NileshAm/RoboGames-TeamLynx/sheet metal parts/Back horizontal brace.SLDPRT

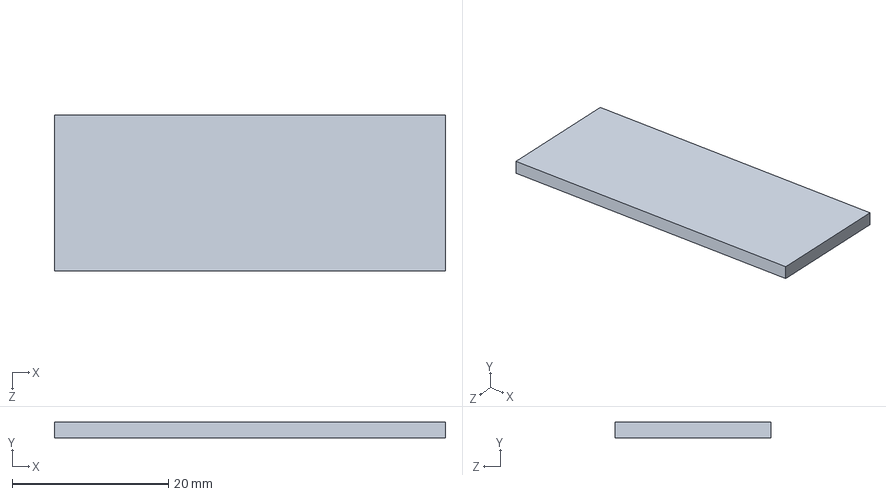
[picture p18: CAD file, 2025-09-17]
sheet metal parts/Back horizontal brace.SLDPRT
50.0 x 2.00 x 20.0 mm
