NileshAm/RoboGames-TeamLynx/downloads/avian-4250-800kv-outrunner-brushless-motor-1.snapshot.3/Outrunner Motor/MotorCrossBar.SLDPRT

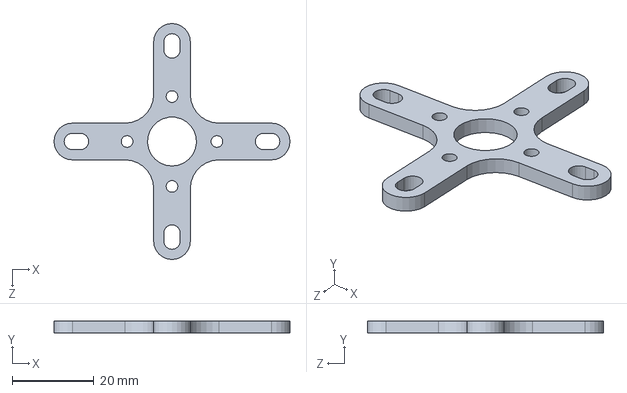
[picture p19: CAD file, 2025-09-02]
downloads/avian-4250-800kv-outrunner-brushless-motor-1.snapshot.3/Outrunner Motor/MotorCrossBar.SLDPRT
57.8 x 3.00 x 57.8 mm
