NileshAm/RoboGames-TeamLynx/laserCutFiles/motor mount sprocket.DXF

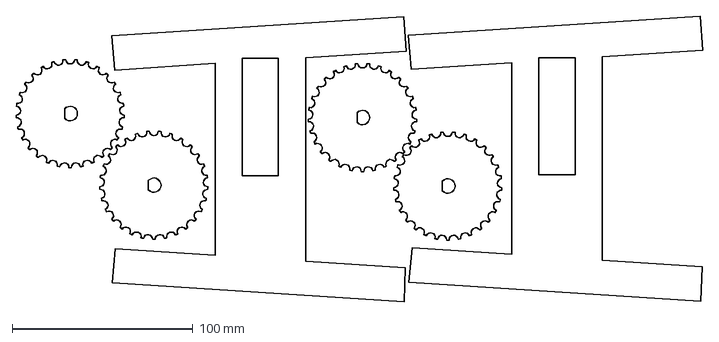
[picture p20: CAD file, 2025-09-11]
laserCutFiles/motor mount sprocket.DXF
380.6 x 158.4 mm
