NileshAm/RoboGames-TeamLynx/Parts/Sproket.SLDPRT

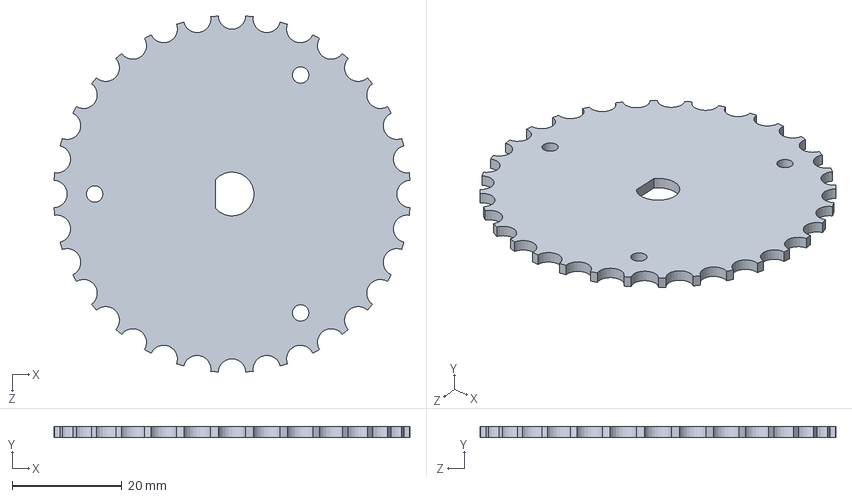
[picture p21: CAD file, 2026-03-14]
Parts/Sproket.SLDPRT
64.8 x 2.00 x 64.8 mm
