NileshAm/RoboGames-TeamLynx/sheet metal parts/Back brace.SLDPRT

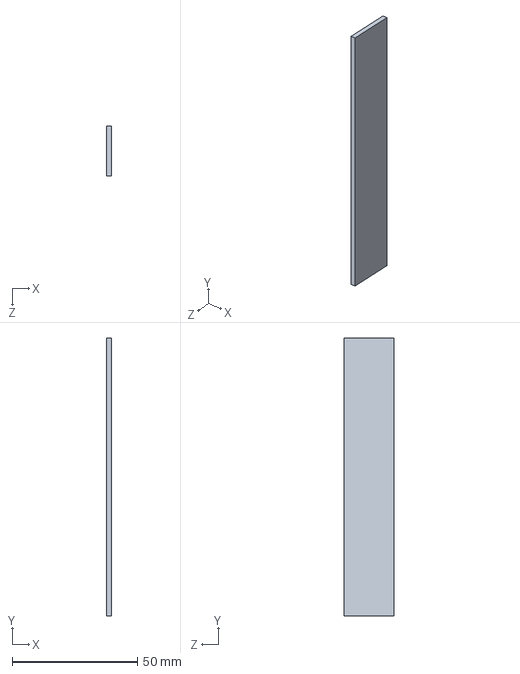
[picture p22: CAD file, 2025-09-17]
sheet metal parts/Back brace.SLDPRT
2.00 x 111.0 x 20.0 mm
