NileshAm/RoboGames-TeamLynx/downloads/avian-4250-800kv-outrunner-brushless-motor-1.snapshot.3/Outrunner Motor/SimpleBearing.SLDPRT

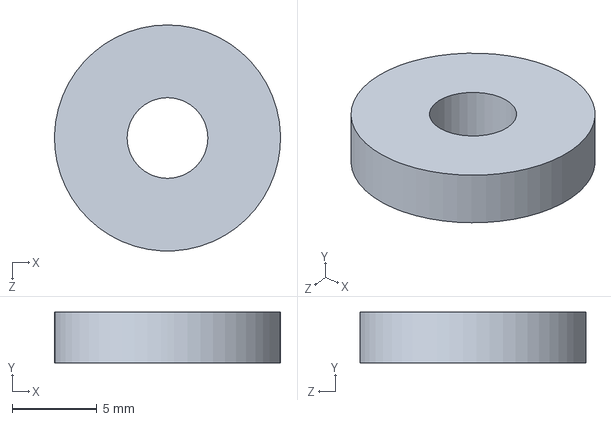
[picture p24: CAD file, 2025-09-02]
downloads/avian-4250-800kv-outrunner-brushless-motor-1.snapshot.3/Outrunner Motor/SimpleBearing.SLDPRT
13.3 x 3.00 x 13.3 mm
