NileshAm/RoboGames-TeamLynx/sheet metal parts/Bottom brace.SLDPRT

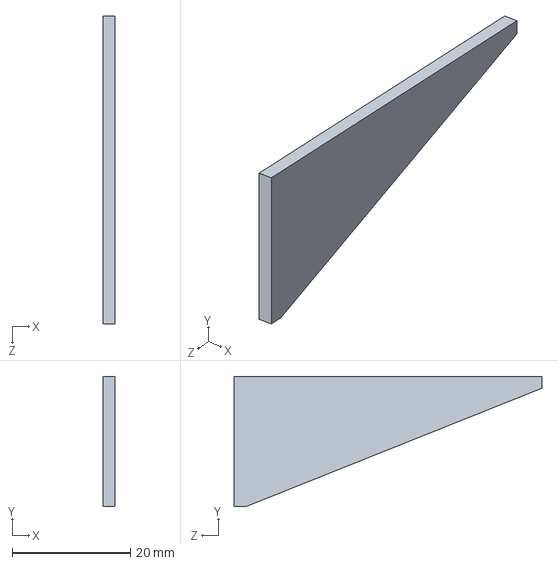
[picture p25: CAD file, 2025-09-17]
sheet metal parts/Bottom brace.SLDPRT
2.00 x 22.0 x 52.0 mm
