NileshAm/RoboGames-TeamLynx/downloads/avian-4250-800kv-outrunner-brushless-motor-1.snapshot.3/Outrunner Motor/Outrunner Brushless Motor Top.SLDPRT

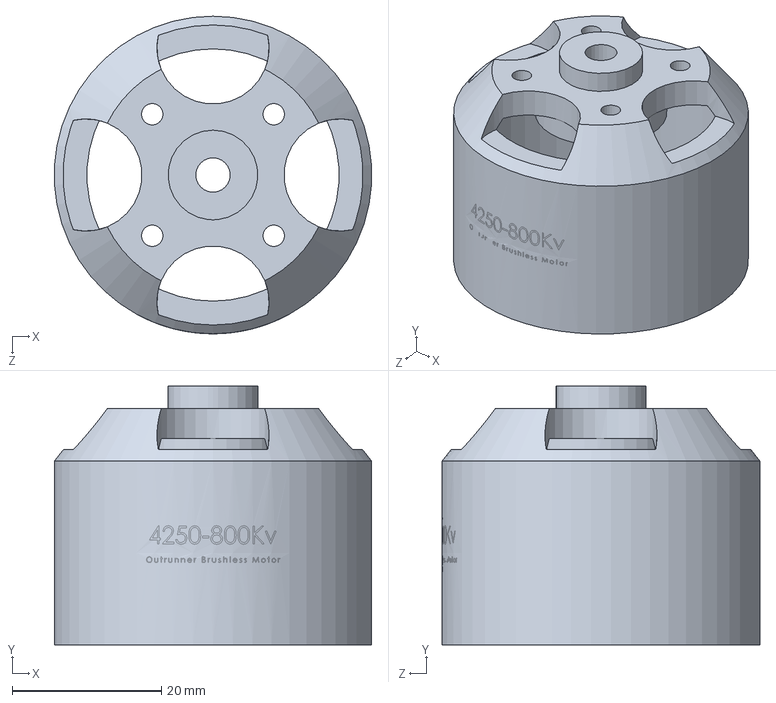
[picture p26: CAD file, 2025-09-02]
downloads/avian-4250-800kv-outrunner-brushless-motor-1.snapshot.3/Outrunner Motor/Outrunner Brushless Motor Top.SLDPRT
42.4 x 34.6 x 42.5 mm
