NileshAm/RoboGames-TeamLynx/downloads/avian-4250-800kv-outrunner-brushless-motor-1.snapshot.3/Outrunner Motor/PropShaft.SLDPRT

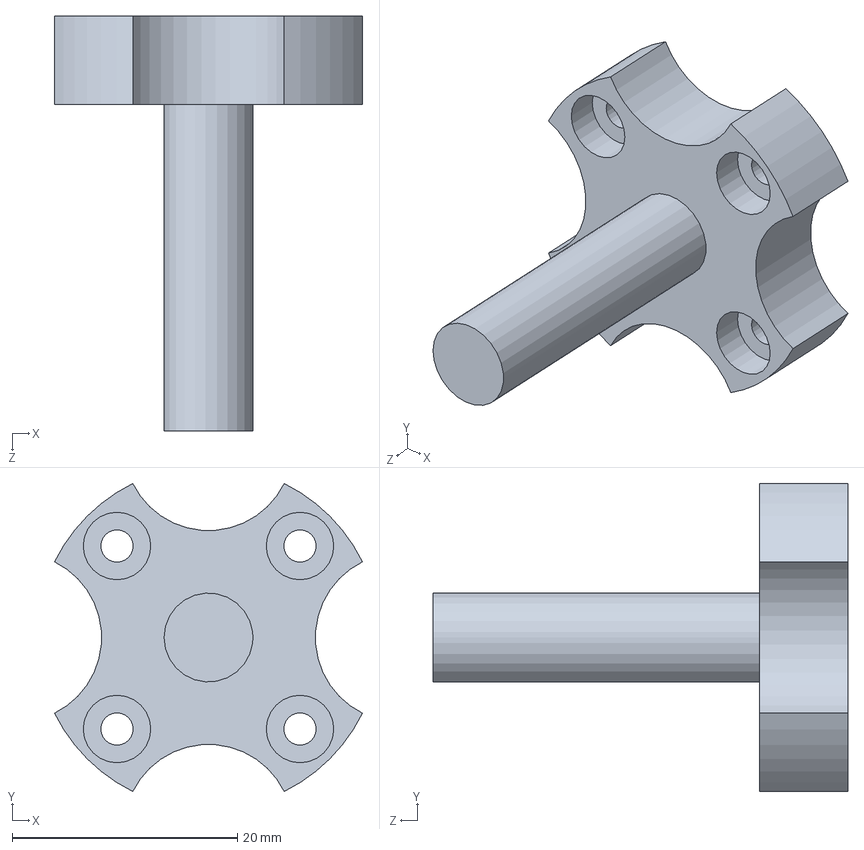
[picture p28: CAD file, 2025-09-02]
downloads/avian-4250-800kv-outrunner-brushless-motor-1.snapshot.3/Outrunner Motor/PropShaft.SLDPRT
27.4 x 27.4 x 36.9 mm
