NileshAm/RoboGames-TeamLynx/Parts/BladeMotorMount.SLDPRT

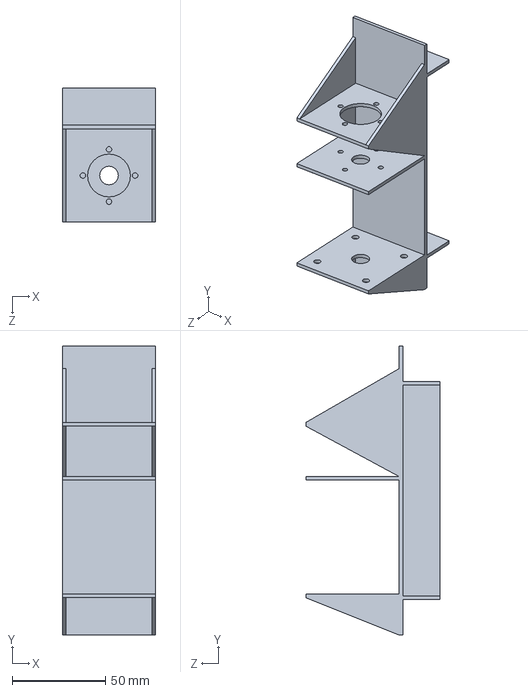
[picture p29: CAD file, 2025-09-17]
Parts/BladeMotorMount.SLDPRT
50.0 x 155.0 x 72.0 mm
