NileshAm/RoboGames-TeamLynx/sheet metal parts/Top brace.SLDPRT

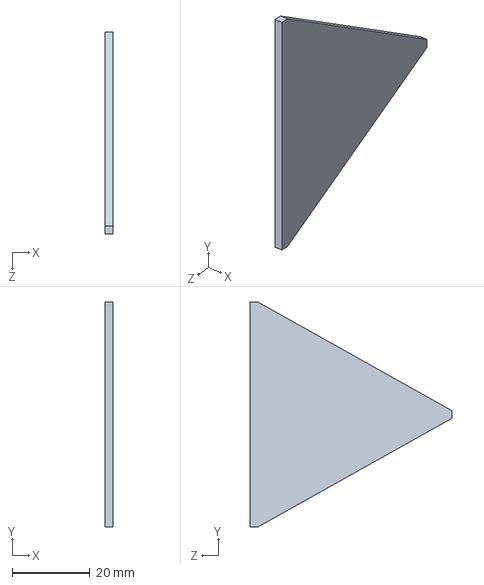
[picture p30: CAD file, 2025-09-17]
sheet metal parts/Top brace.SLDPRT
2.00 x 58.0 x 52.0 mm
