NileshAm/RoboGames-TeamLynx/sheet metal parts/motor mount level 2.SLDPRT

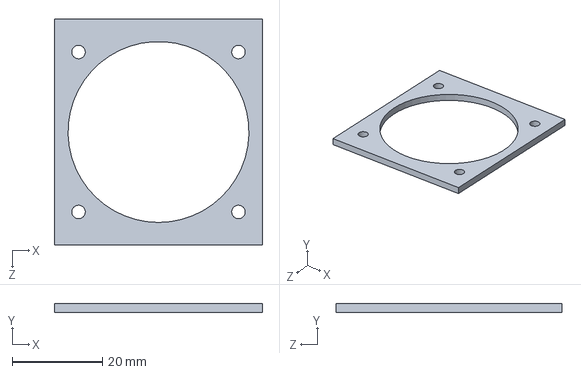
[picture p31: CAD file, 2025-09-17]
sheet metal parts/motor mount level 2.SLDPRT
46.0 x 2.00 x 50.0 mm
