NileshAm/RoboGames-TeamLynx/Parts/motor mount.SLDPRT

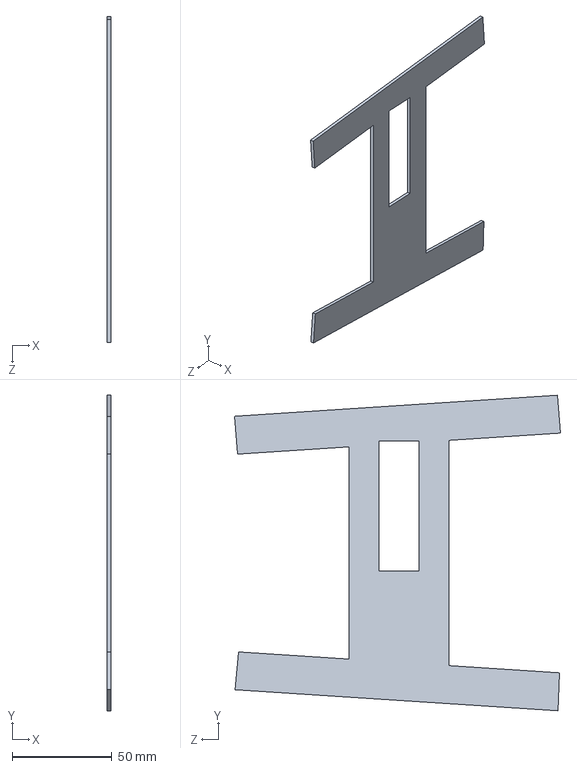
[picture p32: CAD file, 2025-09-11]
Parts/motor mount.SLDPRT
2.00 x 157.9 x 163.2 mm
