NileshAm/RoboGames-TeamLynx/Parts/Wheel.SLDPRT

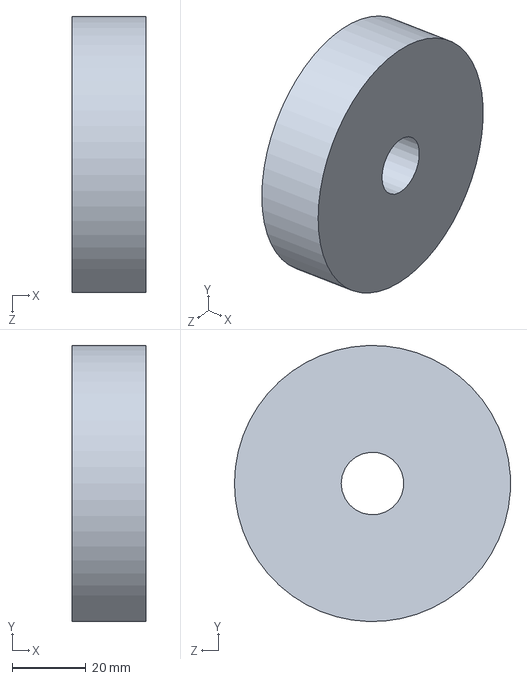
[picture p33: CAD file, 2025-09-11]
Parts/Wheel.SLDPRT
20.0 x 75.0 x 75.0 mm
