NileshAm/RoboGames-TeamLynx/Parts/WheelMotorMountBack.SLDPRT

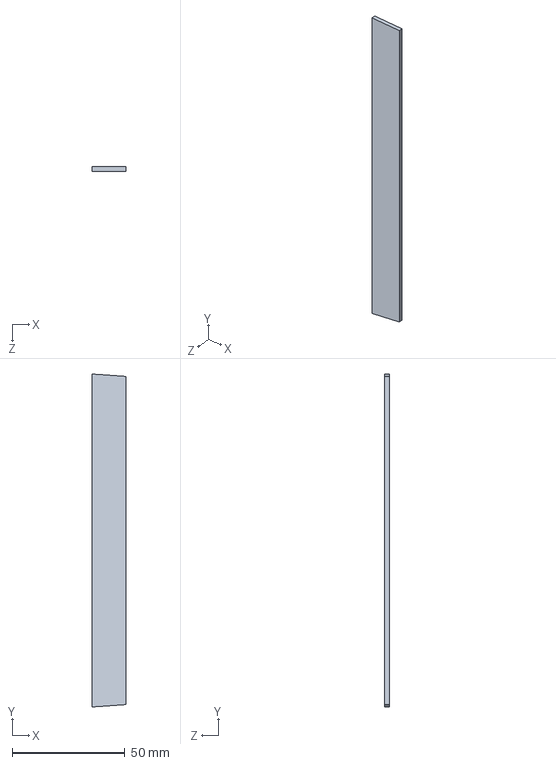
[picture p34: CAD file, 2025-09-02]
Parts/WheelMotorMountBack.SLDPRT
15.0 x 147.4 x 2.00 mm
