NileshAm/RoboGames-TeamLynx/Parts/WheelMotor.SLDPRT

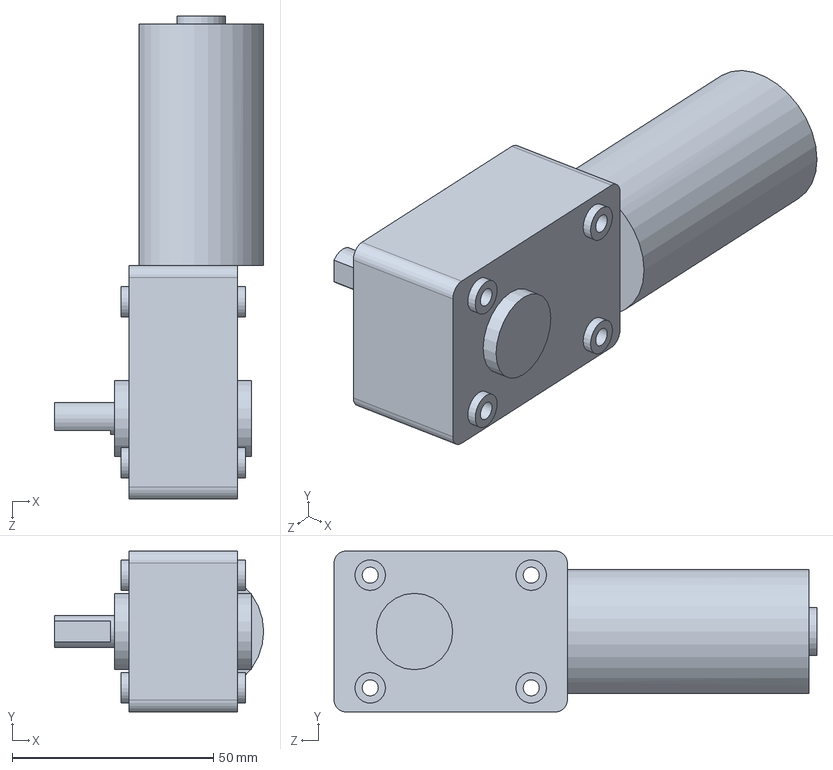
[picture p35: CAD file, 2025-09-02]
Parts/WheelMotor.SLDPRT
52.0 x 40.0 x 120.0 mm
