NileshAm/RoboGames-TeamLynx/Parts/BladeMotorPulley.SLDPRT

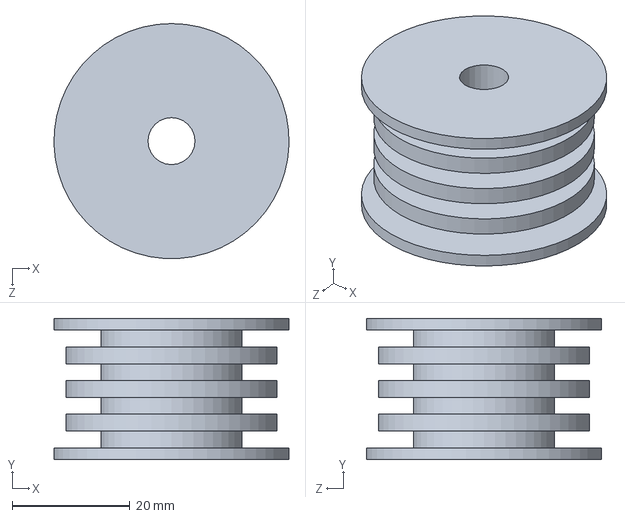
[picture p36: CAD file, 2025-09-02]
Parts/BladeMotorPulley.SLDPRT
40.0 x 24.0 x 40.0 mm
