NileshAm/RoboGames-TeamLynx/Parts/BladeShaft.SLDPRT

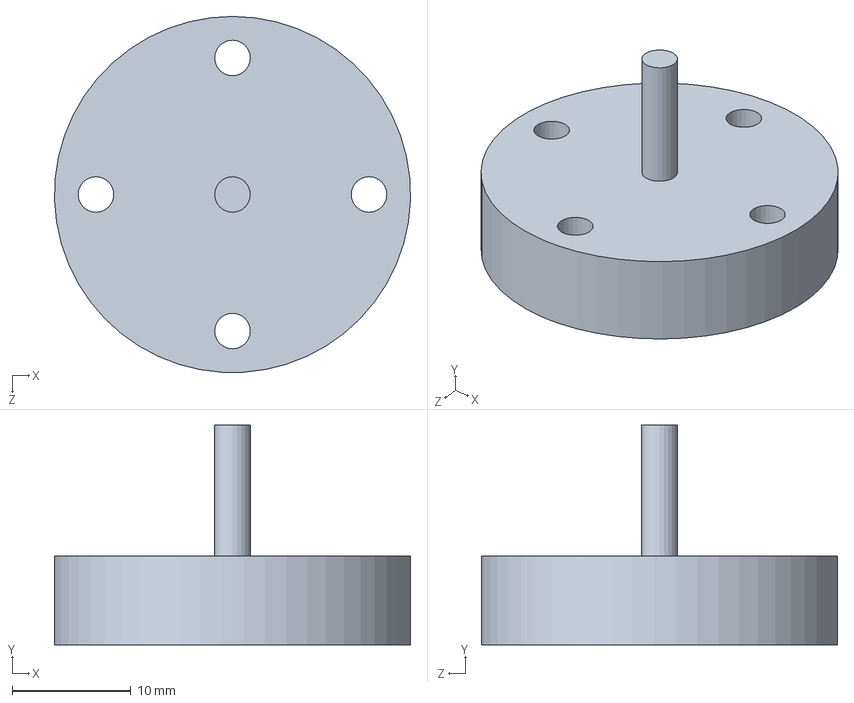
[picture p37: CAD file, 2025-09-02]
Parts/BladeShaft.SLDPRT
30.0 x 18.5 x 30.0 mm
