NileshAm/RoboGames-TeamLynx/Parts/Gearbox.SLDPRT

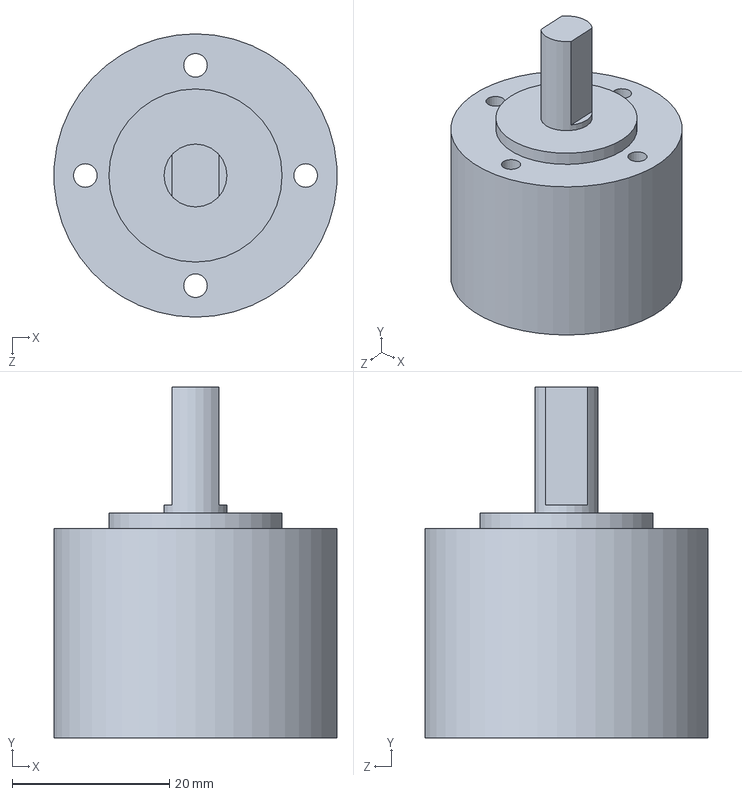
[picture p38: CAD file, 2025-09-02]
Parts/Gearbox.SLDPRT
35.9 x 44.6 x 36.0 mm
